lab11/ACmepp/contiki/apps/zeros/zeros.c

/**
 * \addtogroup cc2538
 * @{
 *
 *
 * @{
 *
 * \file
 *     Example demonstrating the cc2538dk platform
 */
#include "coilcube_ip.h"
#include "contiki-net.h"
#include "contiki.h"
#include "cpu.h"
#include "sys/etimer.h"
#include "sys/rtimer.h"
#include "dev/leds.h"
#include "dev/uart.h"
//#include "dev/relay-button-sensor.h"
#include "dev/watchdog.h"
#include "dev/serial-line.h"
#include "dev/sys-ctrl.h"
#include "net/rime/broadcast.h"
#include "net/ip/uip.h"
#include "net/ip/uip-udp-packet.h"
#include "net/ip/uiplib.h"
#include "net/ipv6/uip-ds6-route.h"
#include "net/ipv6/uip-ds6-nbr.h"
#include <stdio.h>
#include <stdint.h>
#include "dev/nvic.h"
#include "dev/ioc.h"
#include "dev/relay-button-sensor.h"
#include "dev/mac_timer.h"

#include "fm25lb.h"
#include "ade7753.h"
/*---------------------------------------------------------------------------*/
#define LOOP_INTERVAL       CLOCK_SECOND
#define LEDS_OFF_HYSTERISIS (RTIMER_SECOND >> 1)
#define LEDS_PERIODIC       LEDS_YELLOW
#define LEDS_BUTTON         LEDS_RED
#define LEDS_SERIAL_IN      LEDS_ORANGE
#define LEDS_REBOOT         LEDS_ALL
#define LEDS_RF_RX          (LEDS_YELLOW | LEDS_ORANGE)
#define BROADCAST_CHANNEL   129
/*---------------------------------------------------------------------------*/

#define DEBUG 1
#if DEBUG
#include <stdio.h>
#define PRINTF(...) printf(__VA_ARGS__)
#define PRINT6ADDR(addr) PRINTF(" %02x%02x:%02x%02x:%02x%02x:%02x%02x:%02x%02x:%02x%02x:%02x%02x:%02x%02x ", ((uint8_t *)addr)[0], ((uint8_t *)addr)[1], ((uint8_t *)addr)[2], ((uint8_t *)addr)[3], ((uint8_t *)addr)[4], ((uint8_t *)addr)[5], ((uint8_t *)addr)[6], ((uint8_t *)addr)[7], ((uint8_t *)addr)[8], ((uint8_t *)addr)[9], ((uint8_t *)addr)[10], ((uint8_t *)addr)[11], ((uint8_t *)addr)[12], ((uint8_t *)addr)[13], ((uint8_t *)addr)[14], ((uint8_t *)addr)[15])
#define PRINTLLADDR(lladdr) PRINTF(" %02x:%02x:%02x:%02x:%02x:%02x ",lladdr->addr[0], lladdr->addr[1], lladdr->addr[2], lladdr->addr[3],lladdr->addr[4], lladdr->addr[5])
#else
#define PRINTF(...)
#define PRINT6ADDR(addr)
#endif


static uip_ipaddr_t dest_addr;
/*static uip_ipaddr_t bcast_ipaddr;
static uip_lladdr_t bcast_lladdr = {{0, 0, 0, 0, 0, 0, 0, 0}};
static struct uip_udp_conn *client_conn;*/

//pkt_data_t pkt_data = {PROFILE_ID, SEHNSOR_VERSION, 0, 0};

static struct etimer periodic_timer;

static struct simple_udp_connection udp_conn;
static struct simple_udp_connection udp_conn_cc;


fram_config_t config;

uint32_t zero_crossing_time;
uint32_t last_zero_crossing_time;
uint32_t zc_diff;
uint32_t zero_crossing_over;
uint32_t zero_crossing_over_last;


PROCESS(acme_switch, "Zeroes");
AUTOSTART_PROCESSES(&acme_switch);


// Write the config struct back to the FRAM
static void write_config () {
  fm25lb_write(FRAM_ADDR_CONFIG, sizeof(fram_config_t), (uint8_t*) &config);
}

// Turn the plugged in load on
static void load_on () {
  leds_on(LEDS_BLUE);
  GPIO_SET_PIN(RELAY_CTRL_BASE, RELAY_CTRL_MASK);
  config.power_state = RELAY_ON;
  write_config();
}

// Turn the plugged in load off
static void load_off () {
  leds_off(LEDS_BLUE);
  GPIO_CLR_PIN(RELAY_CTRL_BASE, RELAY_CTRL_MASK);
  config.power_state = RELAY_OFF;
  write_config();
}

static void load_toggle () {
  if (config.power_state == RELAY_OFF) load_on();
  else load_off();
}

// Turn the plugged load to the given power state
static void load_set (uint8_t on_off) {
  if (on_off == RELAY_ON) load_on();
  else if (on_off == RELAY_OFF) load_off();
}

static void
receiver(struct simple_udp_connection *c,
         const uip_ipaddr_t *sender_addr,
         uint16_t sender_port,
         const uip_ipaddr_t *receiver_addr,
         uint16_t receiver_port,
         const uint8_t *data,
         uint16_t datalen) {

  uint8_t command;

  if (datalen == 0) return;

  command = data[0];

  simple_udp_sendto_port(&udp_conn,
    (uint8_t*) "aaabbbcccdddeeefffggghhfdsafdafdsafdbfdabffdsafdsafdsafdsa", 1,
    sender_addr, UDP_PORT_VIRT_VOLT);

  switch (command) {
    case ACME_CMD_POWER_ON:
      load_on();
      break;

    case ACME_CMD_POWER_OFF:
      load_off();
      break;

    default:
      break;
  }
}

static void
cc_receiver(struct simple_udp_connection *c,
         const uip_ipaddr_t *sender_addr,
         uint16_t sender_port,
         const uip_ipaddr_t *receiver_addr,
         uint16_t receiver_port,
         const uint8_t *data,
         uint16_t datalen) {


  leds_toggle(LEDS_BLUE);

  uip_lladdr_t new_neighbor_ll;
  uip_ipaddr_t s_addr;
  uip_ds6_route_t* r;

  memset(s_addr.u8, 0, 16);
  memcpy(s_addr.u8+8, sender_addr->u8+8, 8);

  // Add a "neighbor" for our custom route
  // Setup the default broadcast route
  //uiplib_ipaddrconv(ADDR_ALL_ROUTERS, &bcast_ipaddr);
  memcpy(new_neighbor_ll.addr, sender_addr->u8+8, 8);
  new_neighbor_ll.addr[0] ^= 0x02;
  uip_ds6_nbr_add(&s_addr, &new_neighbor_ll, 0, NBR_REACHABLE);
  r = uip_ds6_route_add(&s_addr, 128, &s_addr);

  if (r == NULL) {
    leds_toggle(LEDS_RED);
  }

  voltage_data_t pkt;

  pkt.vpeak              = uip_htonl(ade7753_getMaxVoltage());
  pkt.ticks_since_rising = 0; // set to zero for now
  pkt.chksum_balance     = 0;
  pkt.ending             = 0xF0;

  simple_udp_sendto_port(&udp_conn_cc,
                         (uint8_t*) &pkt,
                         sizeof(voltage_data_t),
                         &s_addr,
                         UDP_PORT_VIRT_VOLT);
}


static void periodic () {


/*  struct {
    uint16_t period;
    uint8_t die;
    uint32_t energy;
    uint32_t vpeak;
    uint32_t timelast;
    uint16_t k;
    uint16_t sfdcap;
    uint16_t chksum_balance;
  } __attribute__ ((__packed__)) pktdata;*/




/*  pktdata.period = uip_htons((uint16_t) ade7753_readReg(ADEREG_PERIOD));
  //pktdata.period = uip_htons(zc_diff);
  pktdata.die    = (uint8_t)  ade7753_readReg(ADEREG_DIEREV);
 // pktdata.energy = uip_htonl(ade7753_readReg(ADEREG_AENERGY));
  //pktdata.energy = uip_htonl(zc_diff);
  pktdata.energy = uip_htonl(zero_crossing_over);
 // pktdata.vpeak  = uip_htonl(ade7753_getMaxVoltage());
  pktdata.vpeak  = uip_htonl(zero_crossing_time);
  pktdata.timelast  = uip_htonl(zero_crossing_over_last);
  //pktdata.k      = uip_htons(0xaabb);
  pktdata.k      = 0;
  pktdata.chksum_balance = 0;

  pktdata.ending = 0xF0; // put this at the end so we know its our packet

//  sfd_cap = ((REG(RFCORE_SFR_MTM1) & 0xFF) << 8) | (REG(RFCORE_SFR_MTM0) & 0xFF);
  pktdata.sfdcap = uip_htons(sfd_cap - last_sfd_cap);

  last_sfd_cap = sfd_cap;
*/
 // leds_toggle(LEDS_RED);
//  simple_udp_sendto_port(&udp_conn,
//    (uint8_t*) &pktdata, sizeof(pktdata),
//    &dest_addr, 2333);
}


/*---------------------------------------------------------------------------*/
/*static void
send_handler(process_event_t ev, process_data_t data) {
  pkt_data.counter++;
  pkt_data.seq_no++;

  leds_toggle(LEDS_BLUE);



  // control relay
  if (pkt_data.seq_no & 0x1) {
    GPIO_CLR_PIN(RELAY_CTRL_BASE, RELAY_CTRL_MASK);
    leds_off(LEDS_RED);
  } else {
    GPIO_SET_PIN(RELAY_CTRL_BASE, RELAY_CTRL_MASK);
    leds_on(LEDS_RED);
  }

  simple_udp_send(&udp_conn, (uint8_t*) &pkt_data, sizeof(pkt_data_t));
}*/

void zero_int (uint8_t port, uint8_t pin) {
  zero_crossing_time = mac_timer_get();
  leds_toggle(LEDS_RED);
}

uint64_t get_zero_crossing () {
  return zero_crossing_time;
}


PROCESS_THREAD(acme_switch, ev, data) {


  PROCESS_BEGIN();

  leds_off(LEDS_ALL);
  leds_on(LEDS_RED);

  // Read the FRAM
  fm25lb_read(FRAM_ADDR_CONFIG, sizeof(fram_config_t), (uint8_t*) &config);

  // Check if this is the first boot or not
  if (config.magic_id != MAGICID) {
    // First boot
    config.magic_id = MAGICID;
    config.power_state = RELAY_OFF;
    write_config();
  }

  // Configure the pin that sets the relay to be an output pin
  GPIO_SET_OUTPUT(RELAY_CTRL_BASE, RELAY_CTRL_MASK);
  // Put the load into its previous state
  load_set(config.power_state);

  GPIO_SOFTWARE_CONTROL(GPIO_B_BASE, GPIO_PIN_MASK(0));
  GPIO_SET_INPUT(GPIO_B_BASE, GPIO_PIN_MASK(0));
  GPIO_DETECT_EDGE(GPIO_B_BASE, GPIO_PIN_MASK(0));
  GPIO_TRIGGER_SINGLE_EDGE(GPIO_B_BASE, GPIO_PIN_MASK(0));
  GPIO_DETECT_RISING(GPIO_B_BASE, GPIO_PIN_MASK(0));
  GPIO_ENABLE_INTERRUPT(GPIO_B_BASE, GPIO_PIN_MASK(0));
  ioc_set_over(GPIO_B_NUM, 0, IOC_OVERRIDE_DIS);
  nvic_interrupt_enable(NVIC_INT_GPIO_PORT_B);
  gpio_register_callback(zero_int, GPIO_B_NUM, 0);

  ade7753_readReg(ADEREG_MODE);
  ade7753_readReg(ADEREG_TEMP);
  ade7753_readReg(ADEREG_PERIOD);
  ade7753_readReg(ADEREG_DIEREV);
  ade7753_readReg(ADEREG_VPEAK);



  // Setup the destination address
  uiplib_ipaddrconv(RECEIVER_ADDR, &dest_addr);

  // Register a simple UDP socket
  simple_udp_register(&udp_conn, UDP_LISTEN_PORT, NULL, 0, receiver);

  // Register for UDP listener
  simple_udp_register(&udp_conn_cc, UDP_PORT_VIRT_VOLT, NULL, 0, cc_receiver);

  etimer_set(&periodic_timer, 10*CLOCK_SECOND);

  while(1) {
    PROCESS_YIELD();

    if (etimer_expired(&periodic_timer)) {
      periodic();
      etimer_restart(&periodic_timer);
    } else if (ev == sensors_event) {
      if (data == &relay_button_sensor) {
        load_toggle();
      }
    }
  }

  PROCESS_END();
}
/*---------------------------------------------------------------------------*/
